Nischalm1996/Vibha_garden_sensor/2.FIRMWARE/garden_Arduino/main/sound.h

/* program for soil moisture sensor.
1. begin()  initialise variables
2. int getRawReading()
3. float getMoisturePercentage()*/

#ifndef _SOUND_H
#define _SOUND_H
#include "Arduino.h"


const int soundSensorPin = A3;
const int lowNoiseThreshold = 400;
const int highNoiseThreshold = 1023;

class sound
{
  public:
    int getReading()
    {
        return(analogRead(soundSensorPin));
    }
    float getNoisePercentage()
    {
      return(map(getReading(),lowNoiseThreshold,highNoiseThreshold,100,0));
      return(getReading());
    }
};

#endif //_SOUND_H
