Nischalm1996/Vibha_garden_sensor/2.FIRMWARE/ESP_Arduino/secrets.h

// Use this file to store all of the private credentials 
// and connection details

#define SECRET_SSID "Nischal.M"    // replace MySSID with your WiFi network name
#define SECRET_PASS "nischal@001743"  // replace MyPassword with your WiFi password

#define SECRET_CH_ID 1418539      // replace 0000000 with your channel number
#define SECRET_WRITE_APIKEY "BHV28CL3QOYQV1YD"   // replace XYZ with your channel write API Key
